Midaah-r/keyboard/assets/3ding_quote.png

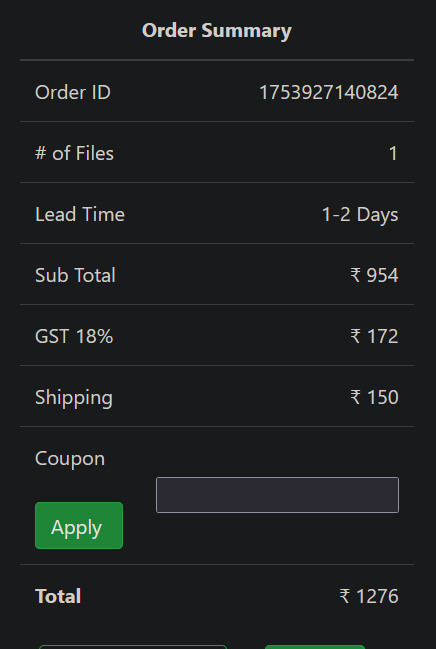
assets/3ding_quote.png
