Midaah-r/keyboard/assets/jlcpcb_quote.png

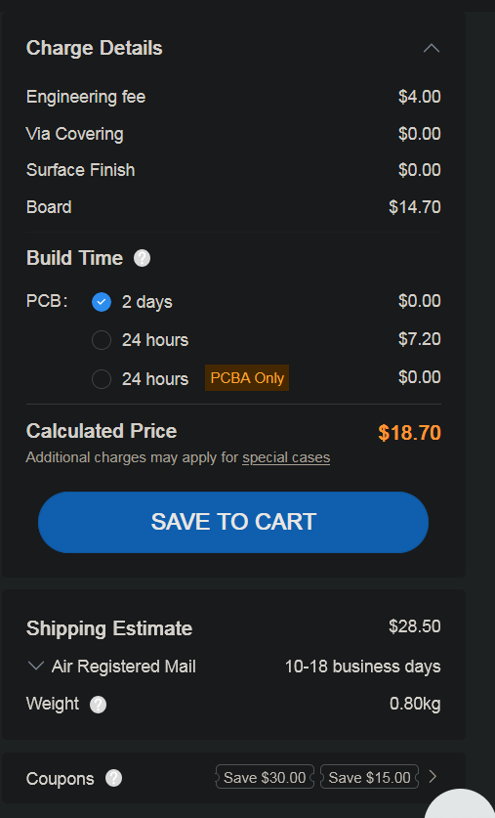
assets/jlcpcb_quote.png
