Midaah-r/keyboard/assets_journal/schematic.png

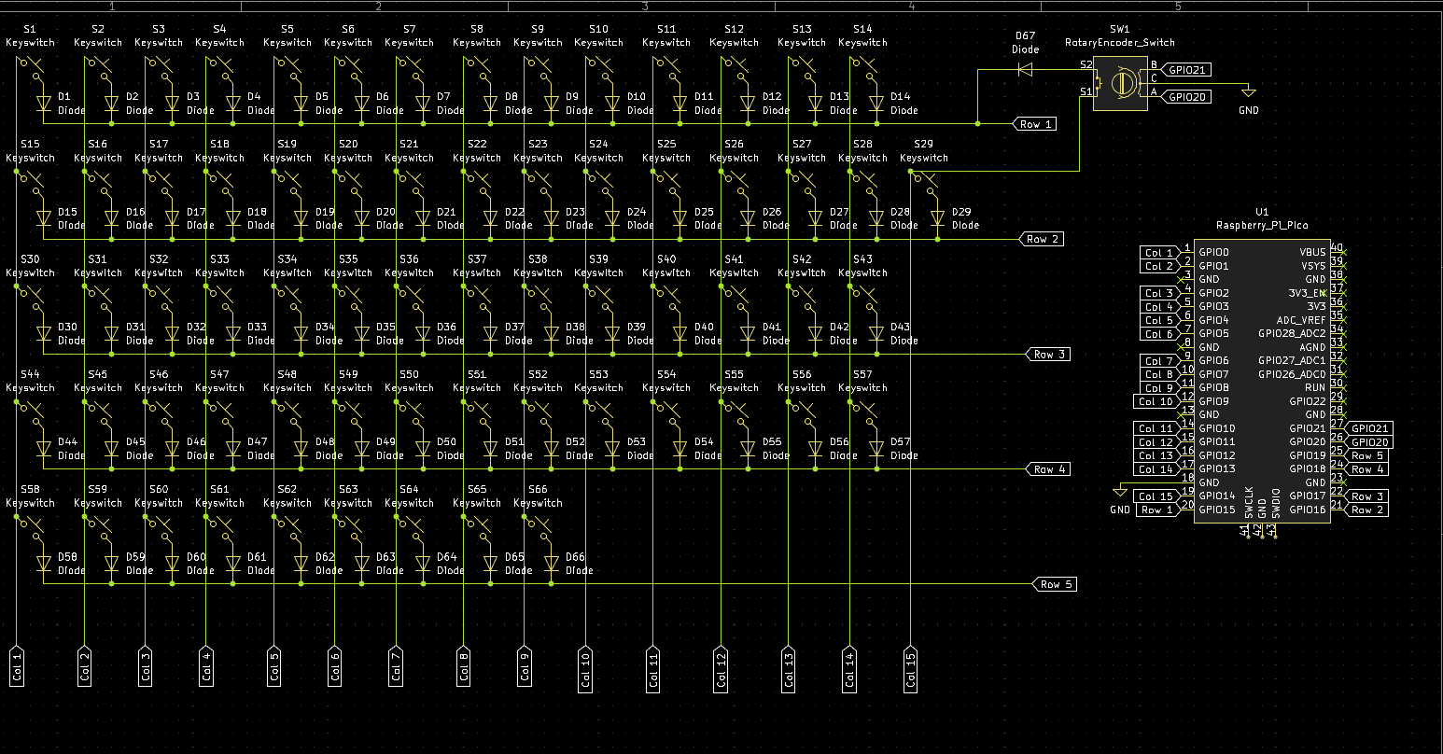
assets_journal/schematic.png
