Midaah-r/keyboard/assets_journal/bottom_case.png

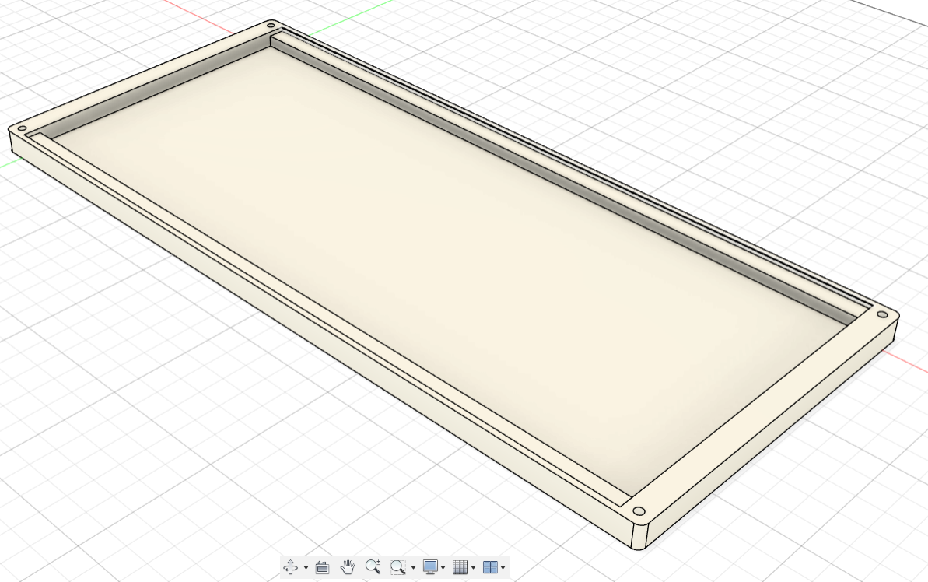
assets_journal/bottom_case.png
