Midaah-r/keyboard/assets_journal/case_net_raw.png

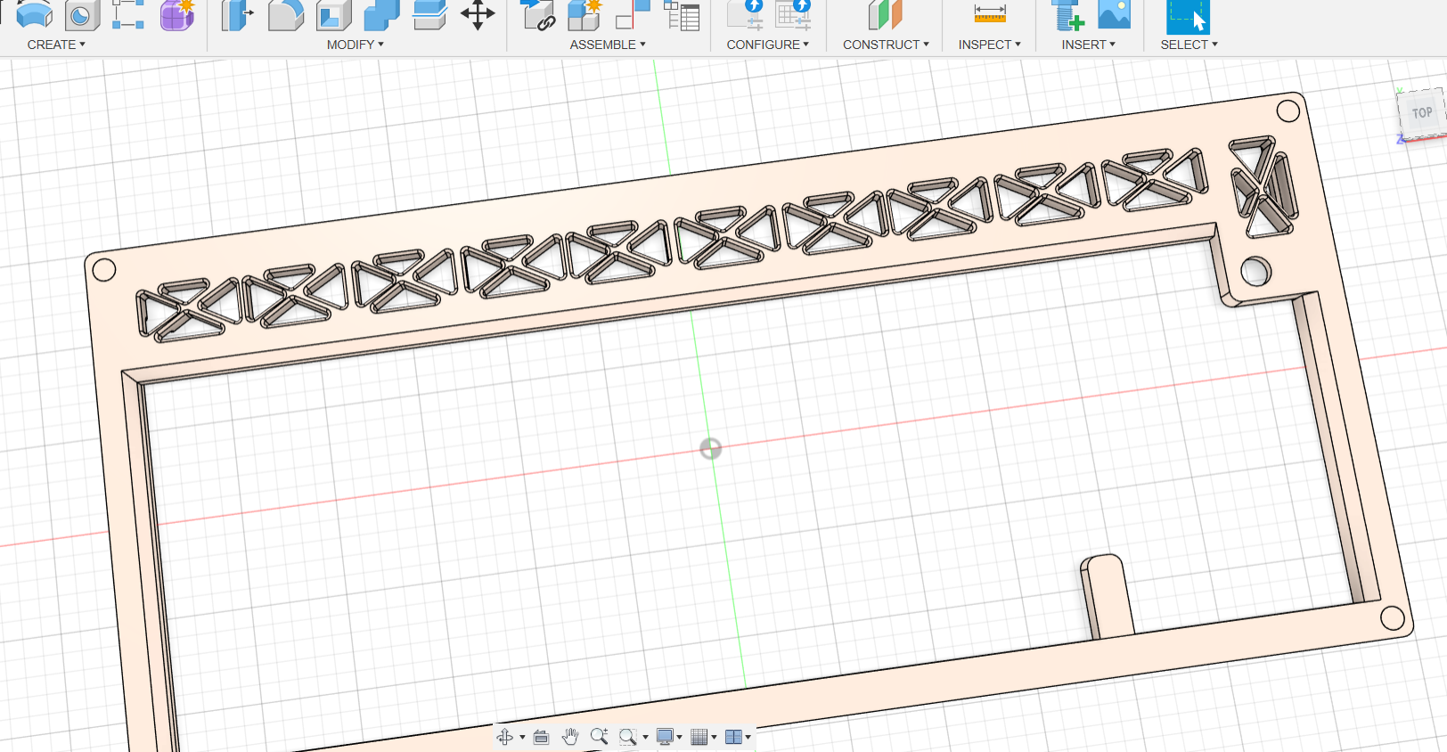
assets_journal/case_net_raw.png
