Midaah-r/keyboard/assets_journal/layout.png

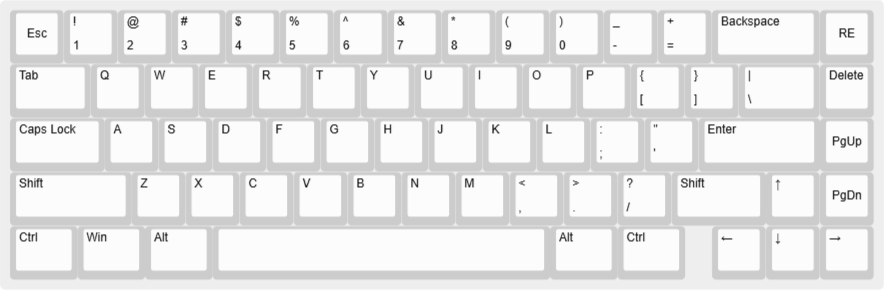
assets_journal/layout.png
