Midaah-r/keyboard/assets_journal/notion.jpg

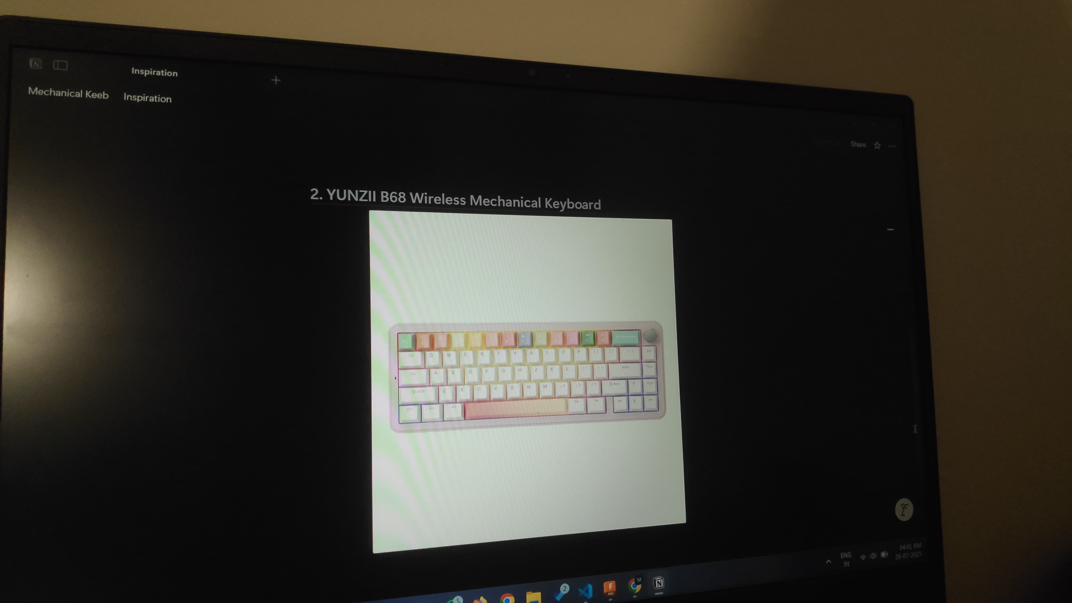
assets_journal/notion.jpg
