Midaah-r/keyboard/assets_journal/pcb_3d.png

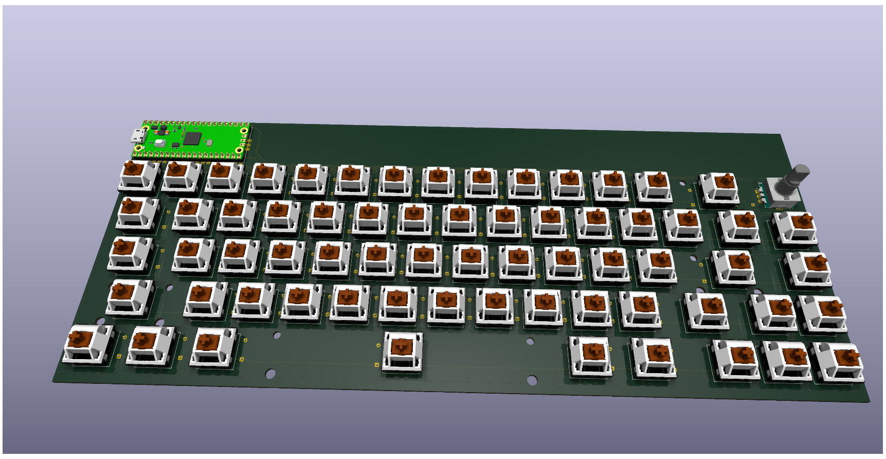
assets_journal/pcb_3d.png
