Midaah-r/keyboard/assets_journal/plate.png

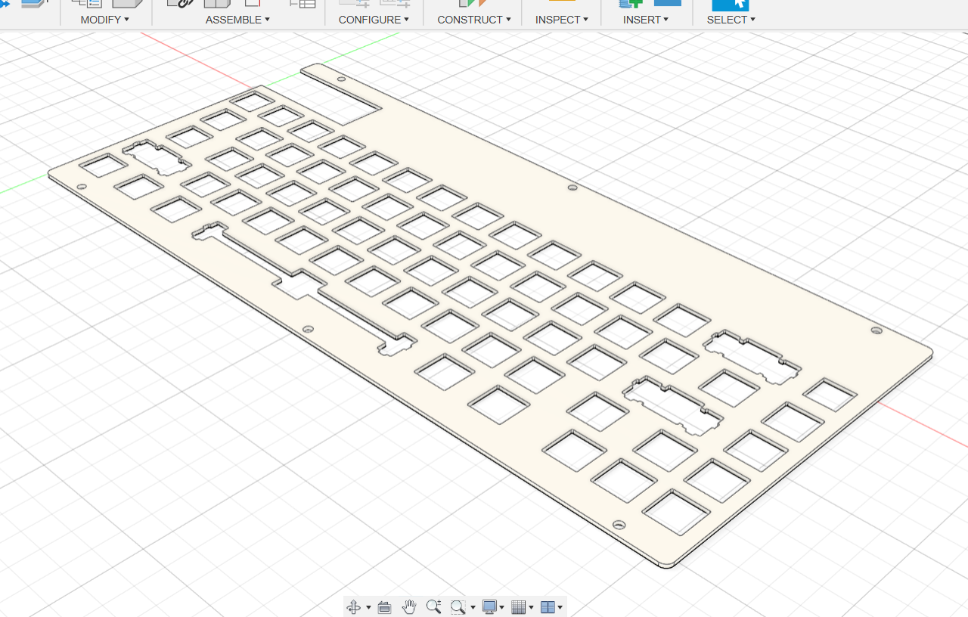
assets_journal/plate.png
