Midaah-r/keyboard/assets_journal/RE_square.png

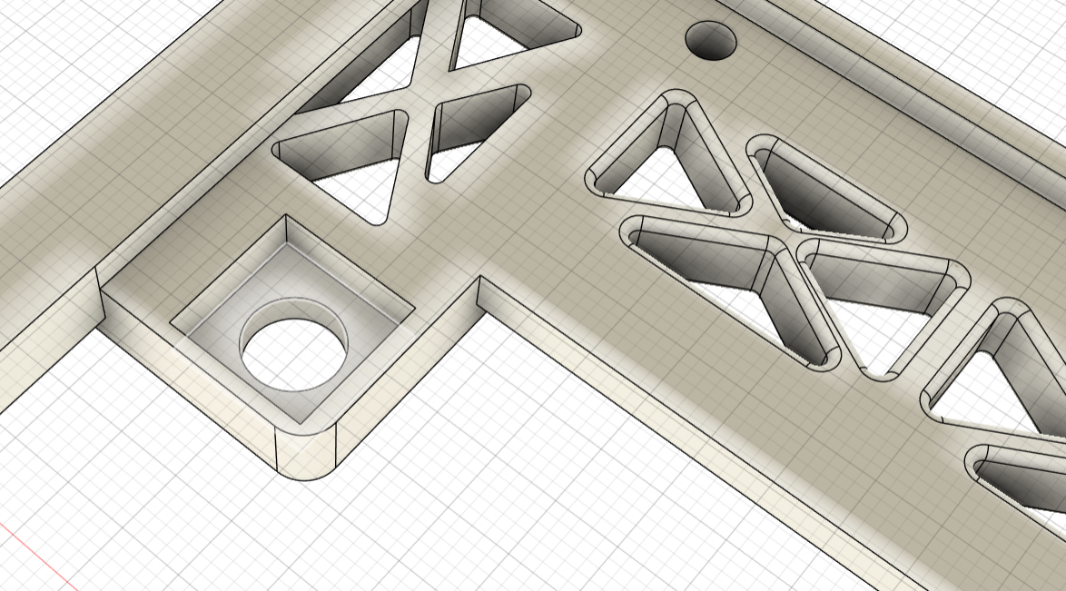
assets_journal/RE_square.png
