Midaah-r/keyboard/assets_journal/top_case.png

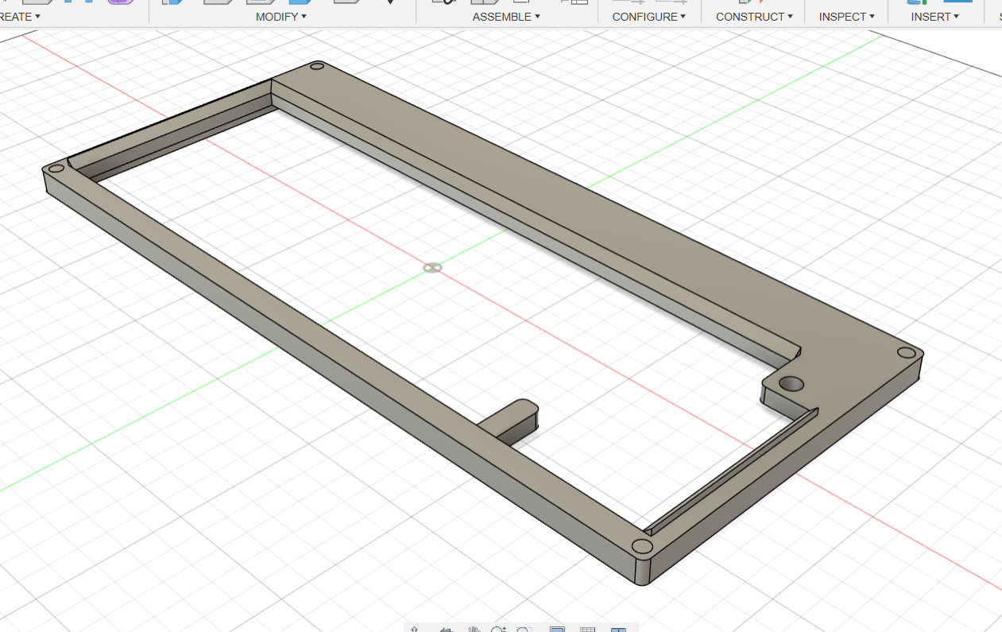
assets_journal/top_case.png
