Midaah-r/keyboard/assets_journal/wings_figma.png

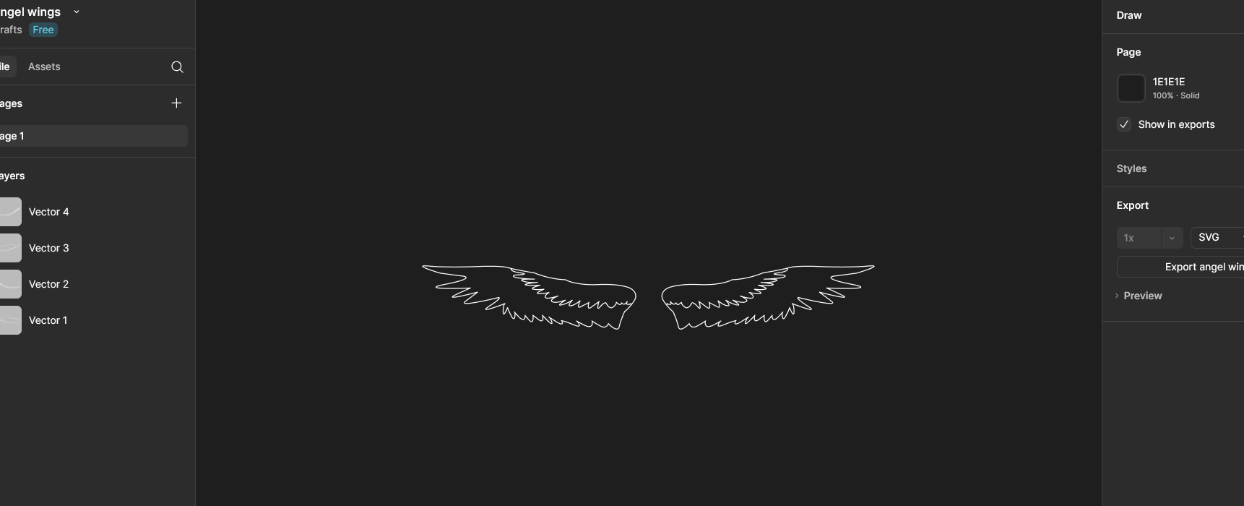
assets_journal/wings_figma.png
